gerryisrad/PocketReference/Docs/Documents & Advanced/PCB/SCRAPPED V3/EXPORTED SVG/3D_BACK.png

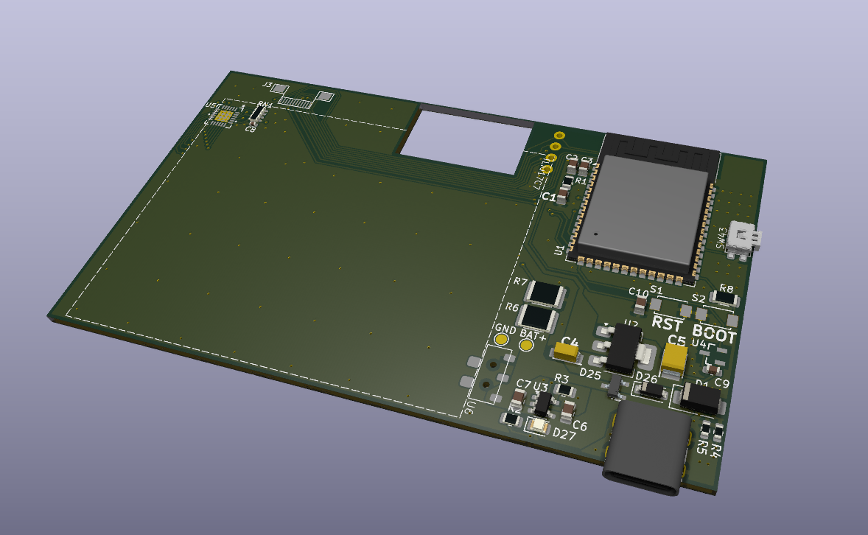
Docs/Documents & Advanced/PCB/SCRAPPED V3/EXPORTED SVG/3D_BACK.png
