gerryisrad/PocketReference/Docs/Documents & Advanced/PCB/V3.3/einkPDA_keyboard/EXPORTED SVG/3D_FRONT.png

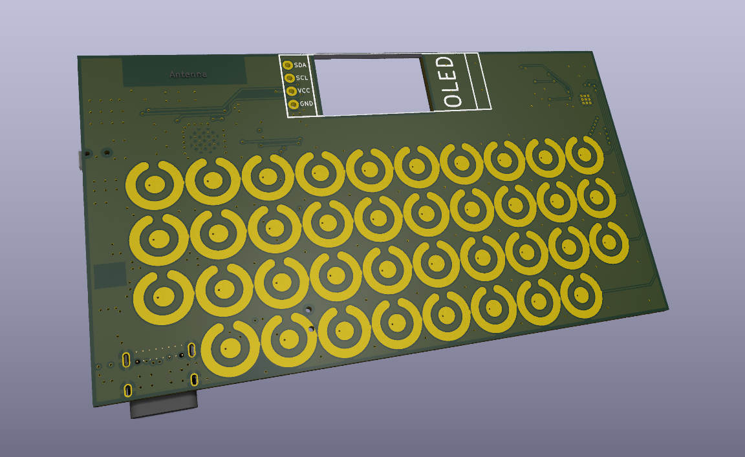
Docs/Documents & Advanced/PCB/V3.3/einkPDA_keyboard/EXPORTED SVG/3D_FRONT.png
