gerryisrad/PocketReference/Docs/Documents & Advanced/PCB/SCRAPPED V3/EXPORTED SVG/B_Cu.png

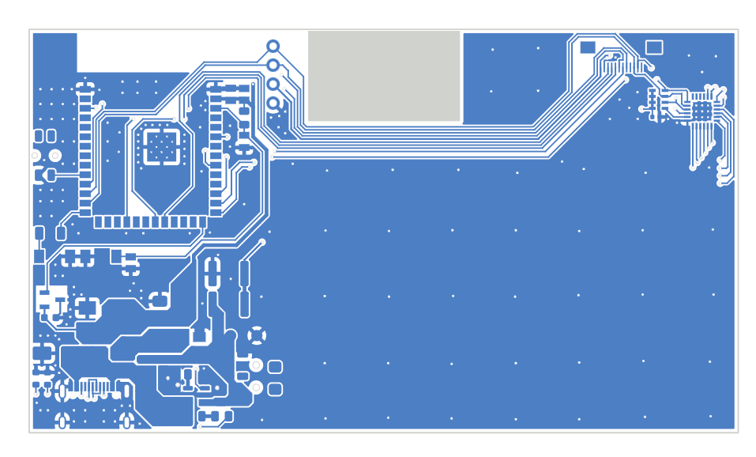
Docs/Documents & Advanced/PCB/SCRAPPED V3/EXPORTED SVG/B_Cu.png
