gerryisrad/PocketReference/Docs/Documents & Advanced/PCB/SCRAPPED V3/EXPORTED SVG/In1.png

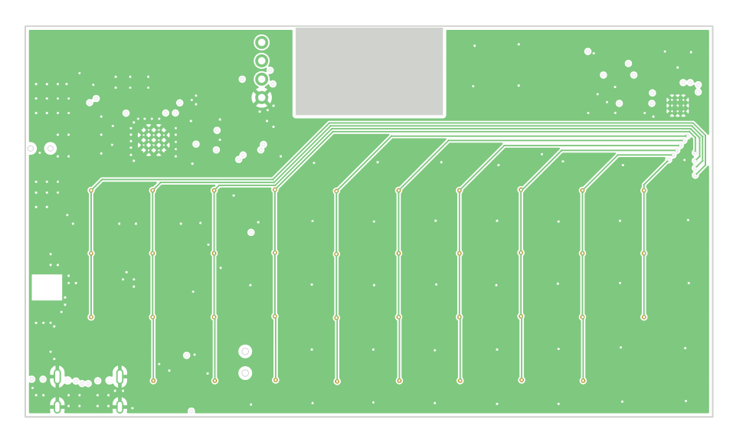
Docs/Documents & Advanced/PCB/SCRAPPED V3/EXPORTED SVG/In1.png
