gerryisrad/PocketReference/Docs/Documents & Advanced/PCB/SCRAPPED V3/EXPORTED SVG/Layout.png

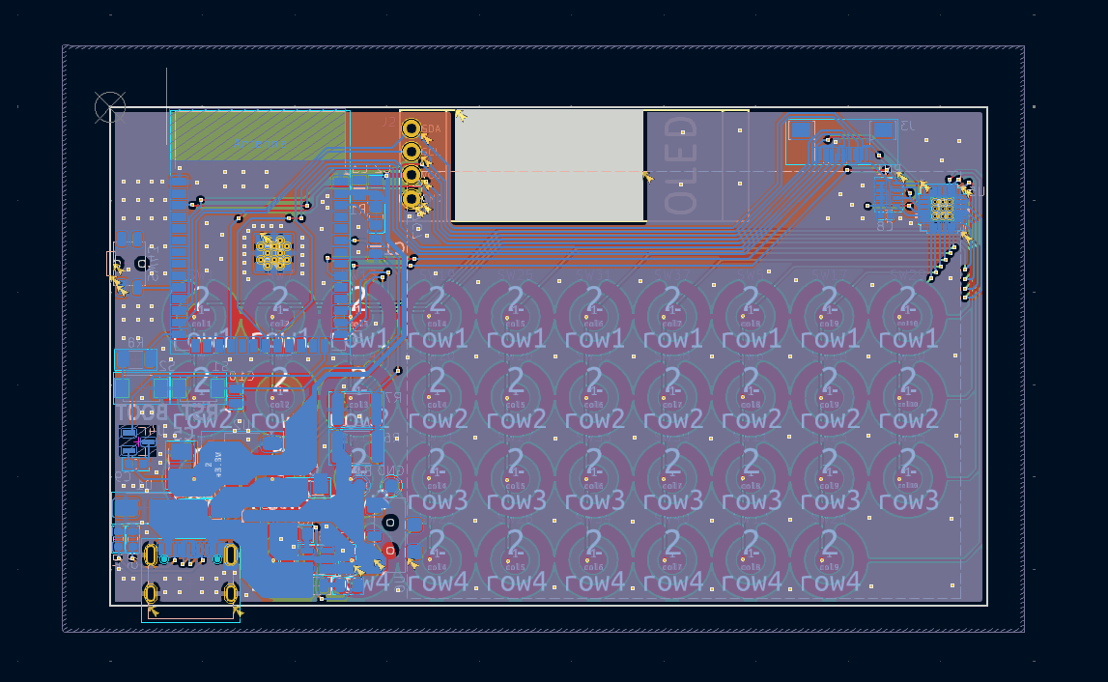
Docs/Documents & Advanced/PCB/SCRAPPED V3/EXPORTED SVG/Layout.png
