gerryisrad/PocketReference/Docs/Documents & Advanced/PCB/V3.2 - Copy/PCB_V3.2.pdf

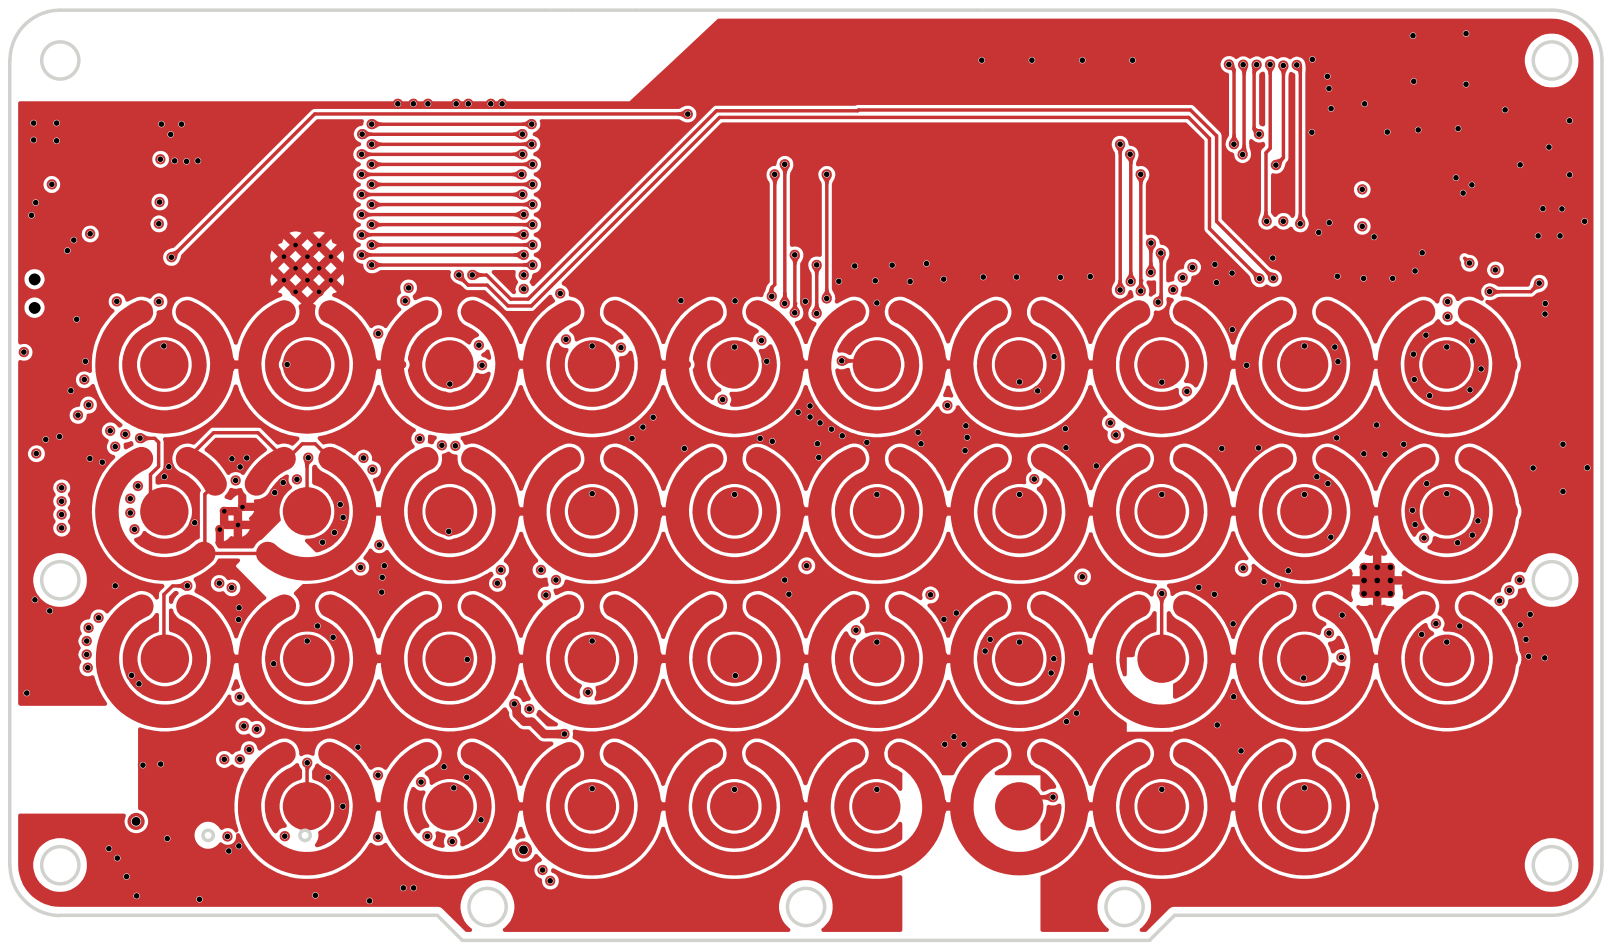
[picture p16: page 1]

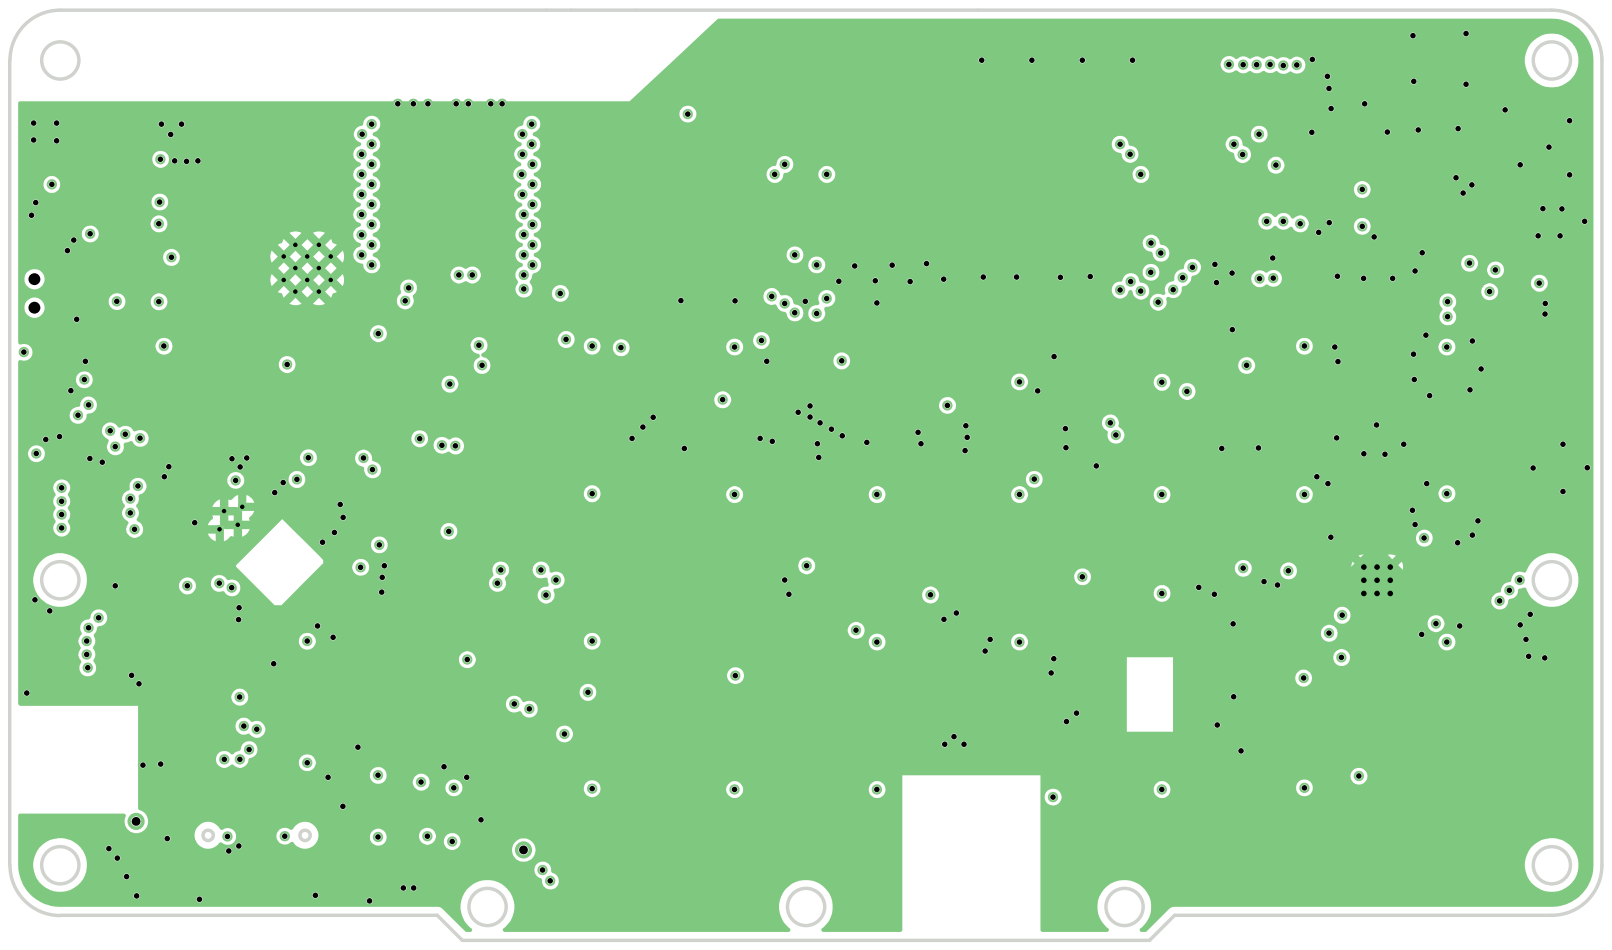
[picture p17: page 2]

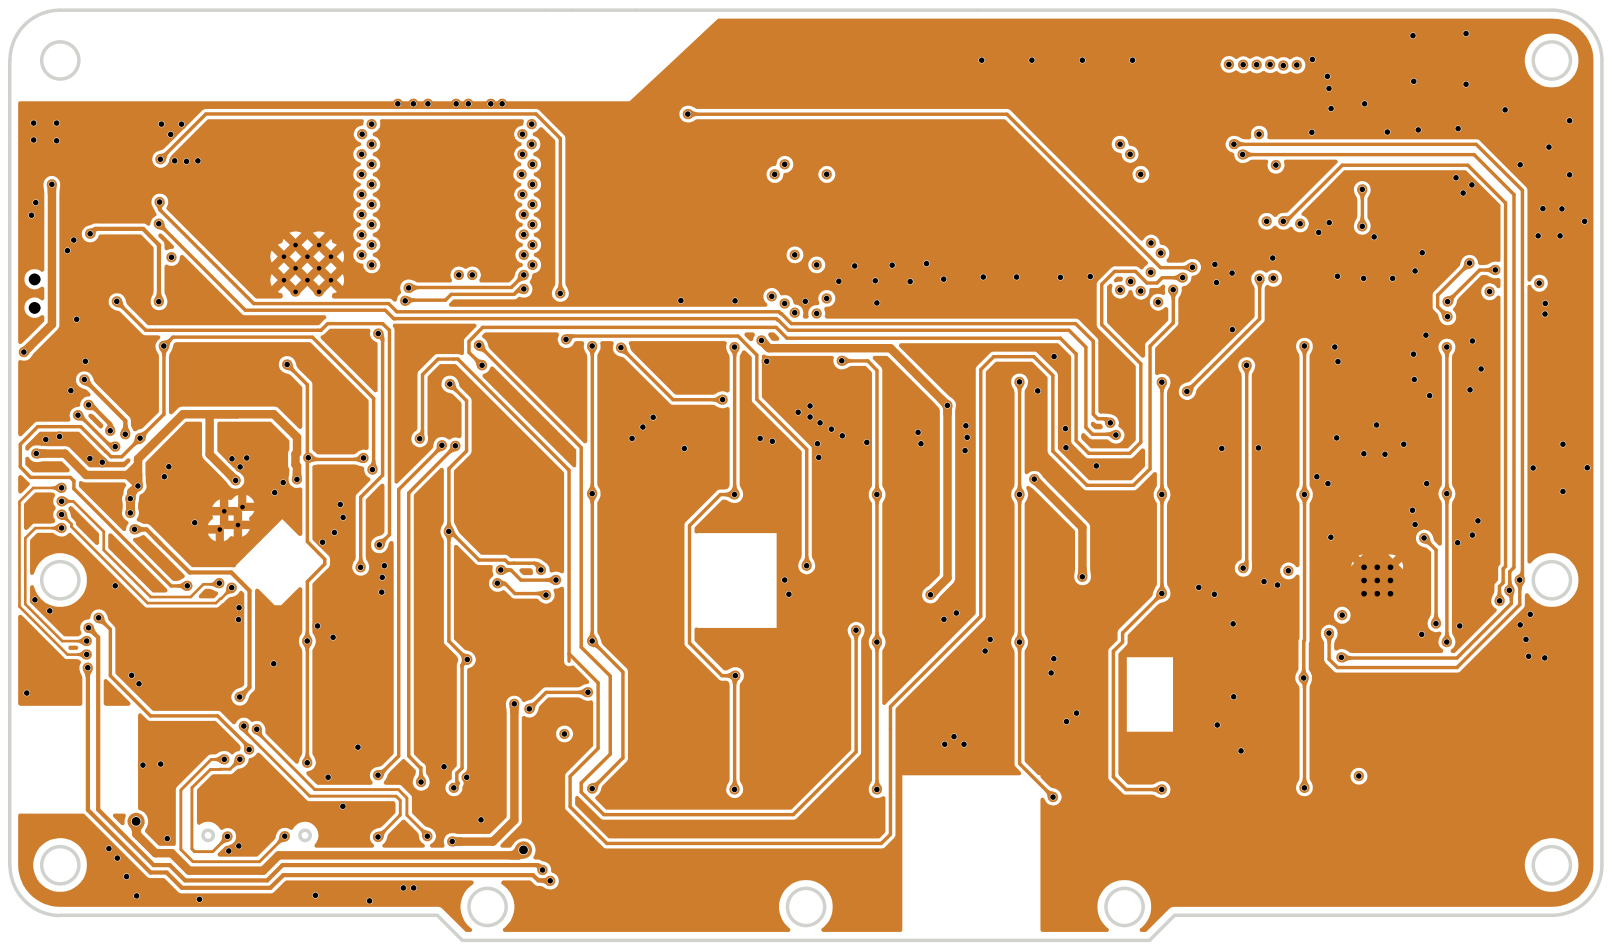
[picture p18: page 3]

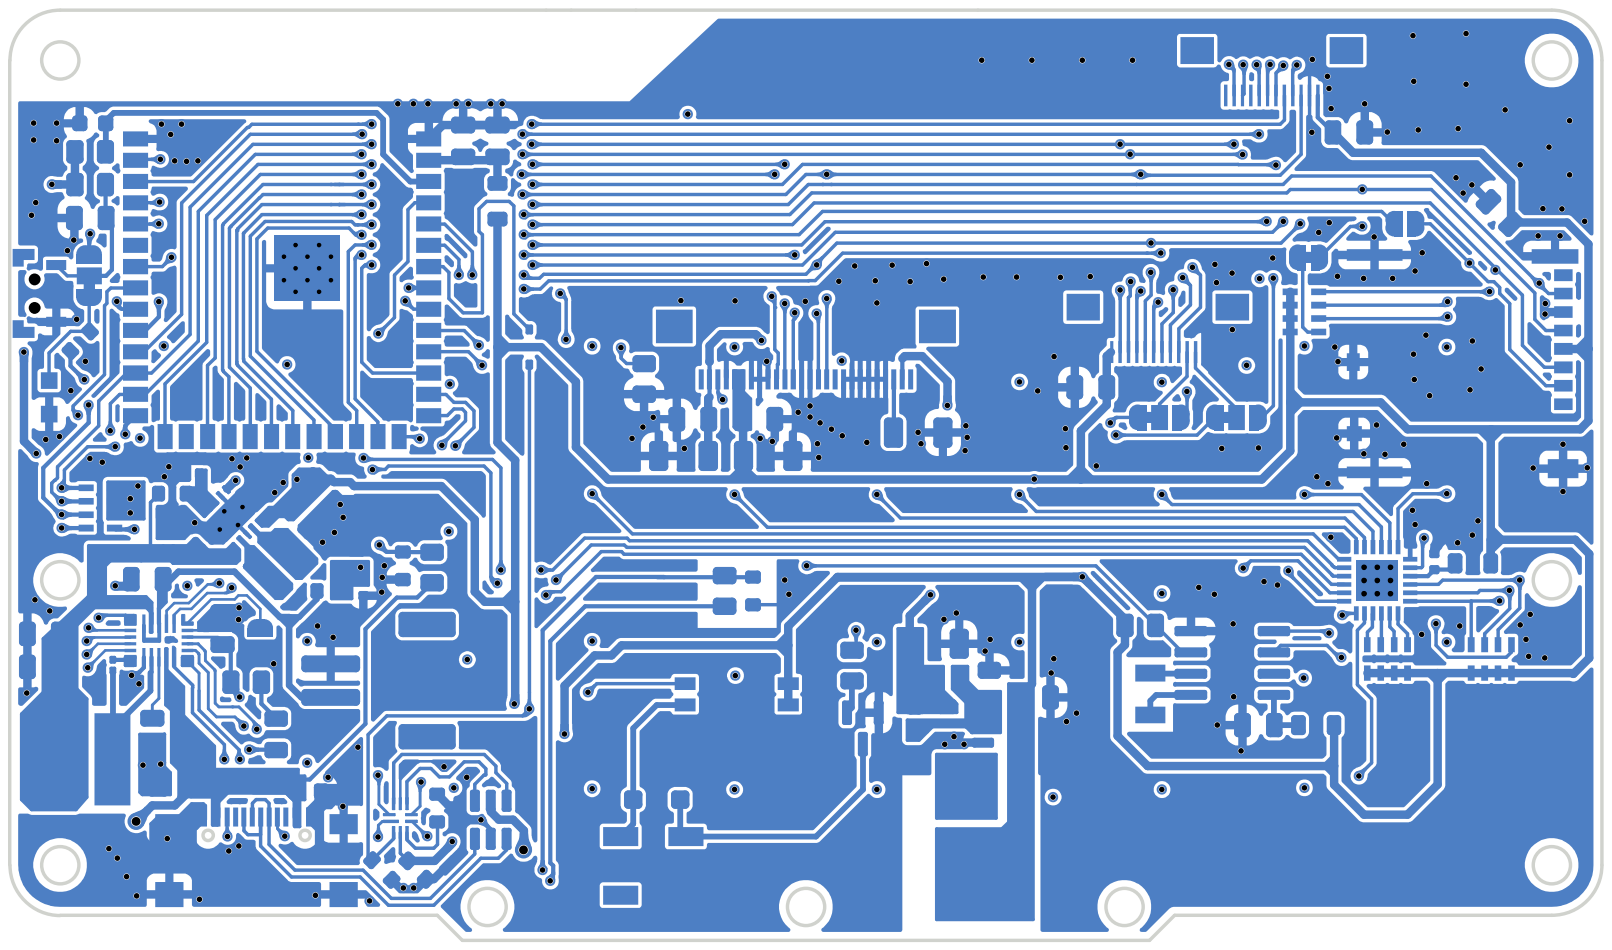
[picture p19: page 4]

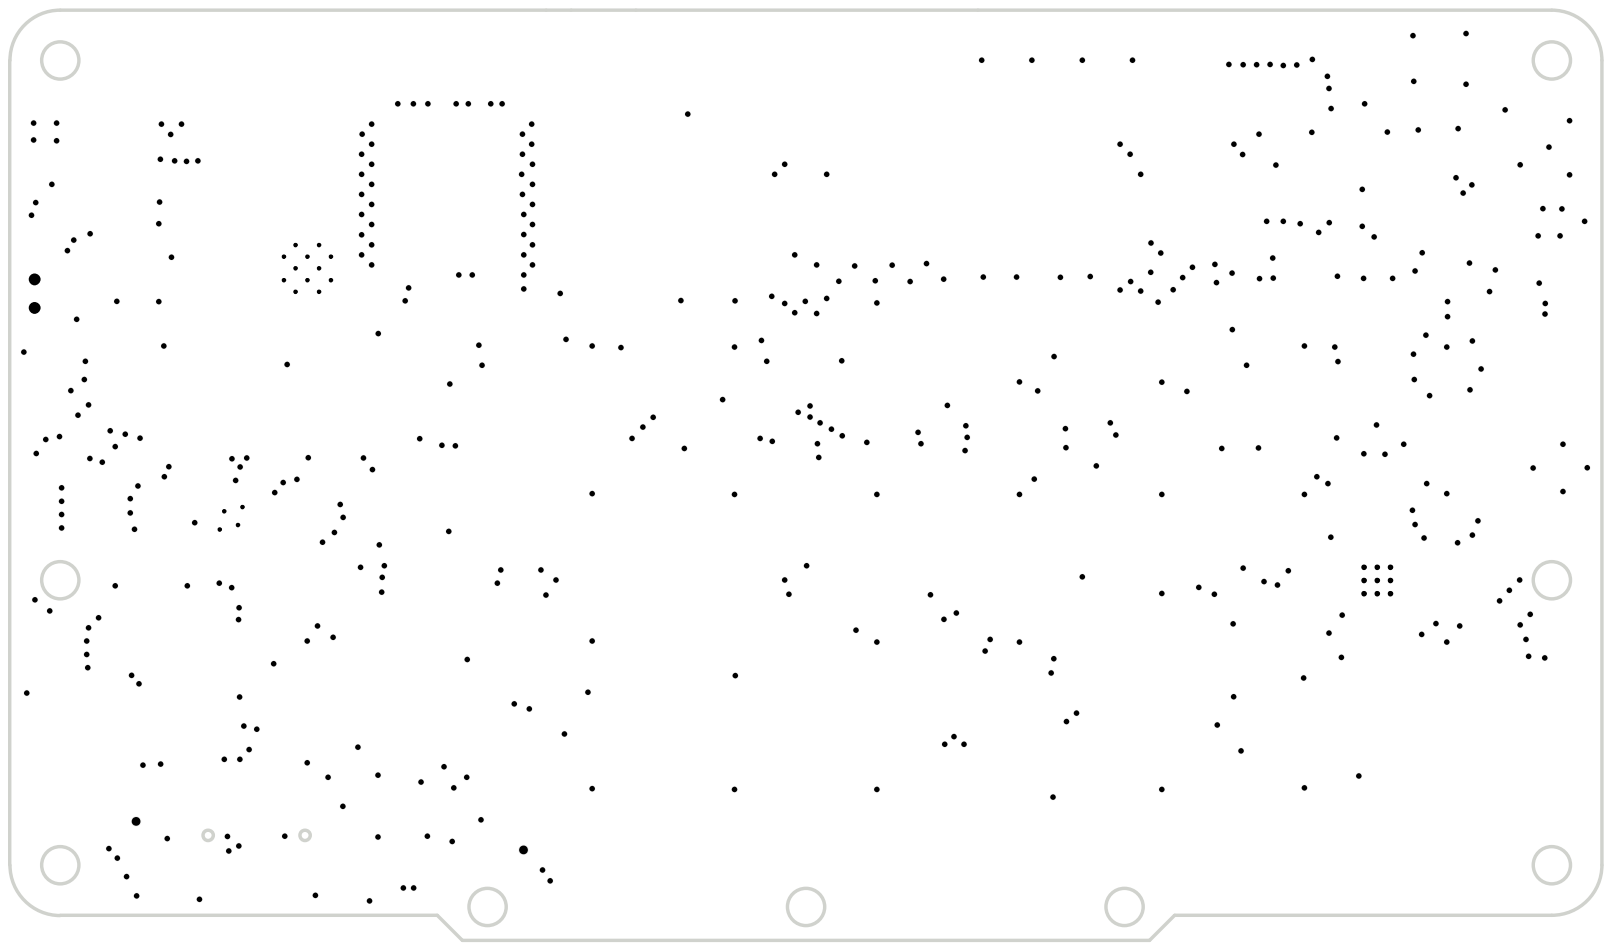
[picture p20: page 5]

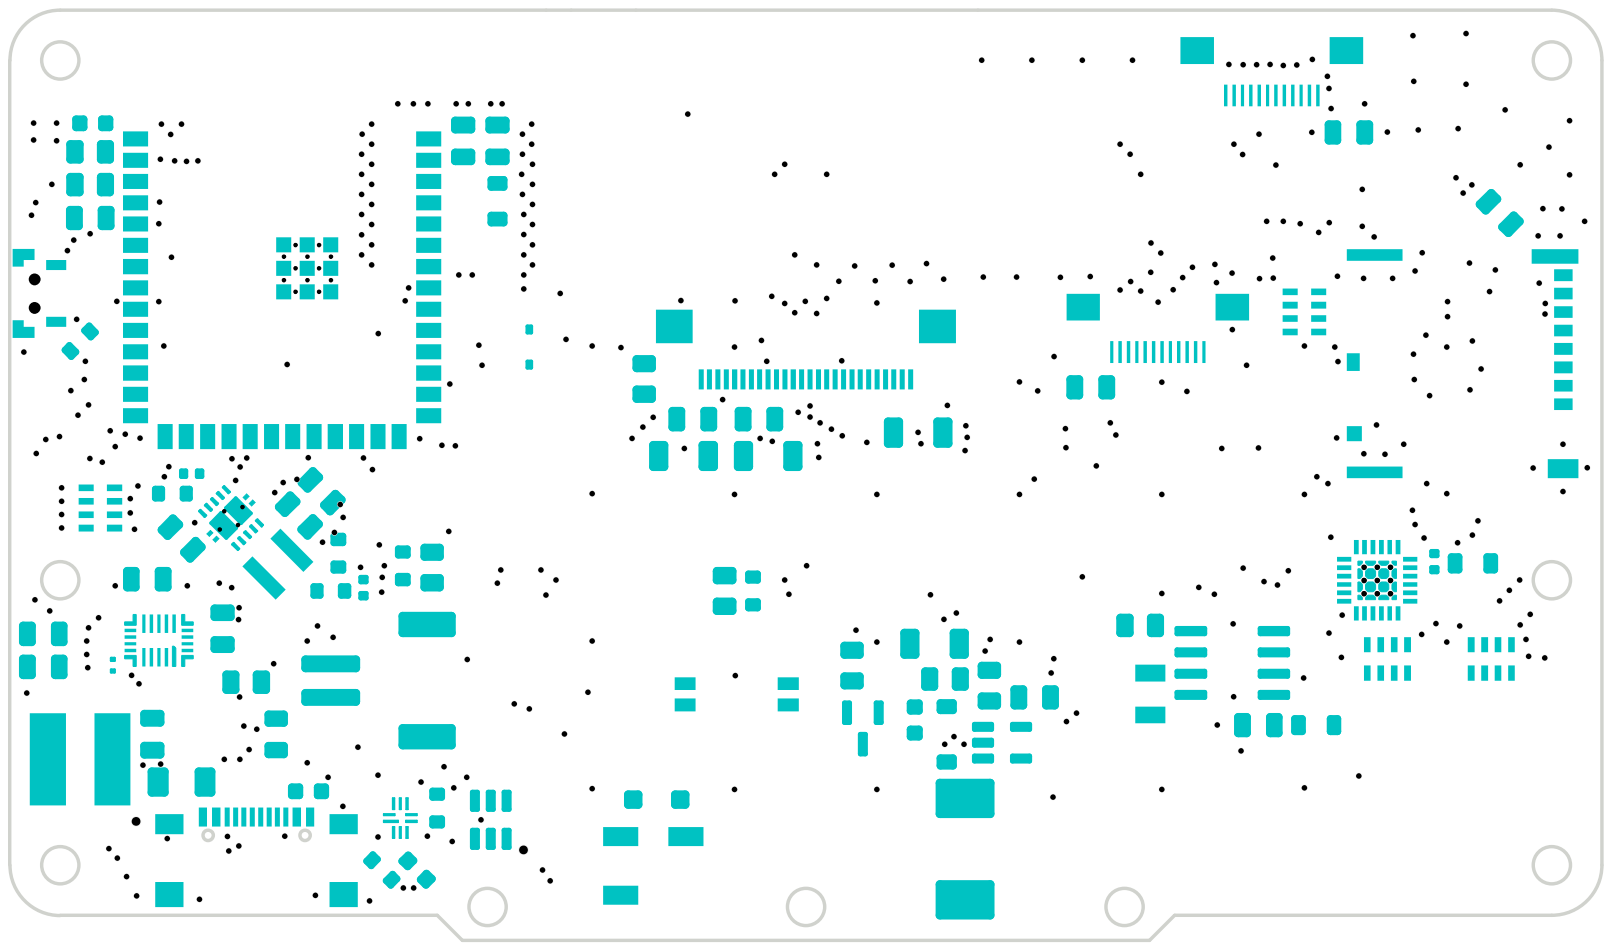
[picture p21: page 6]

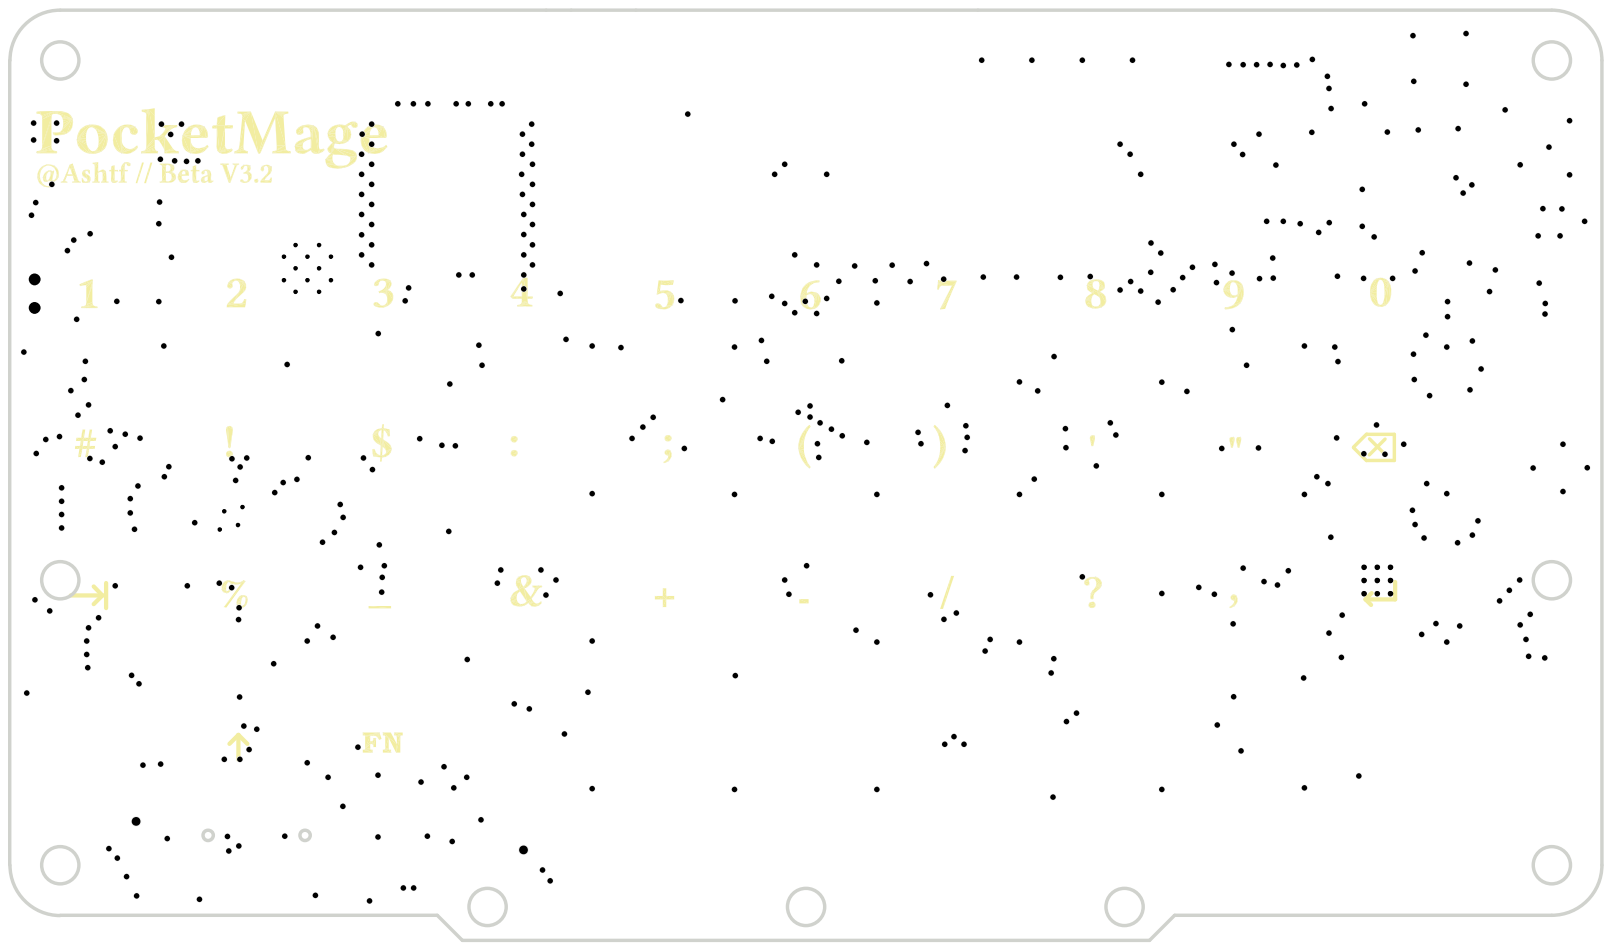
[picture p22: page 7]

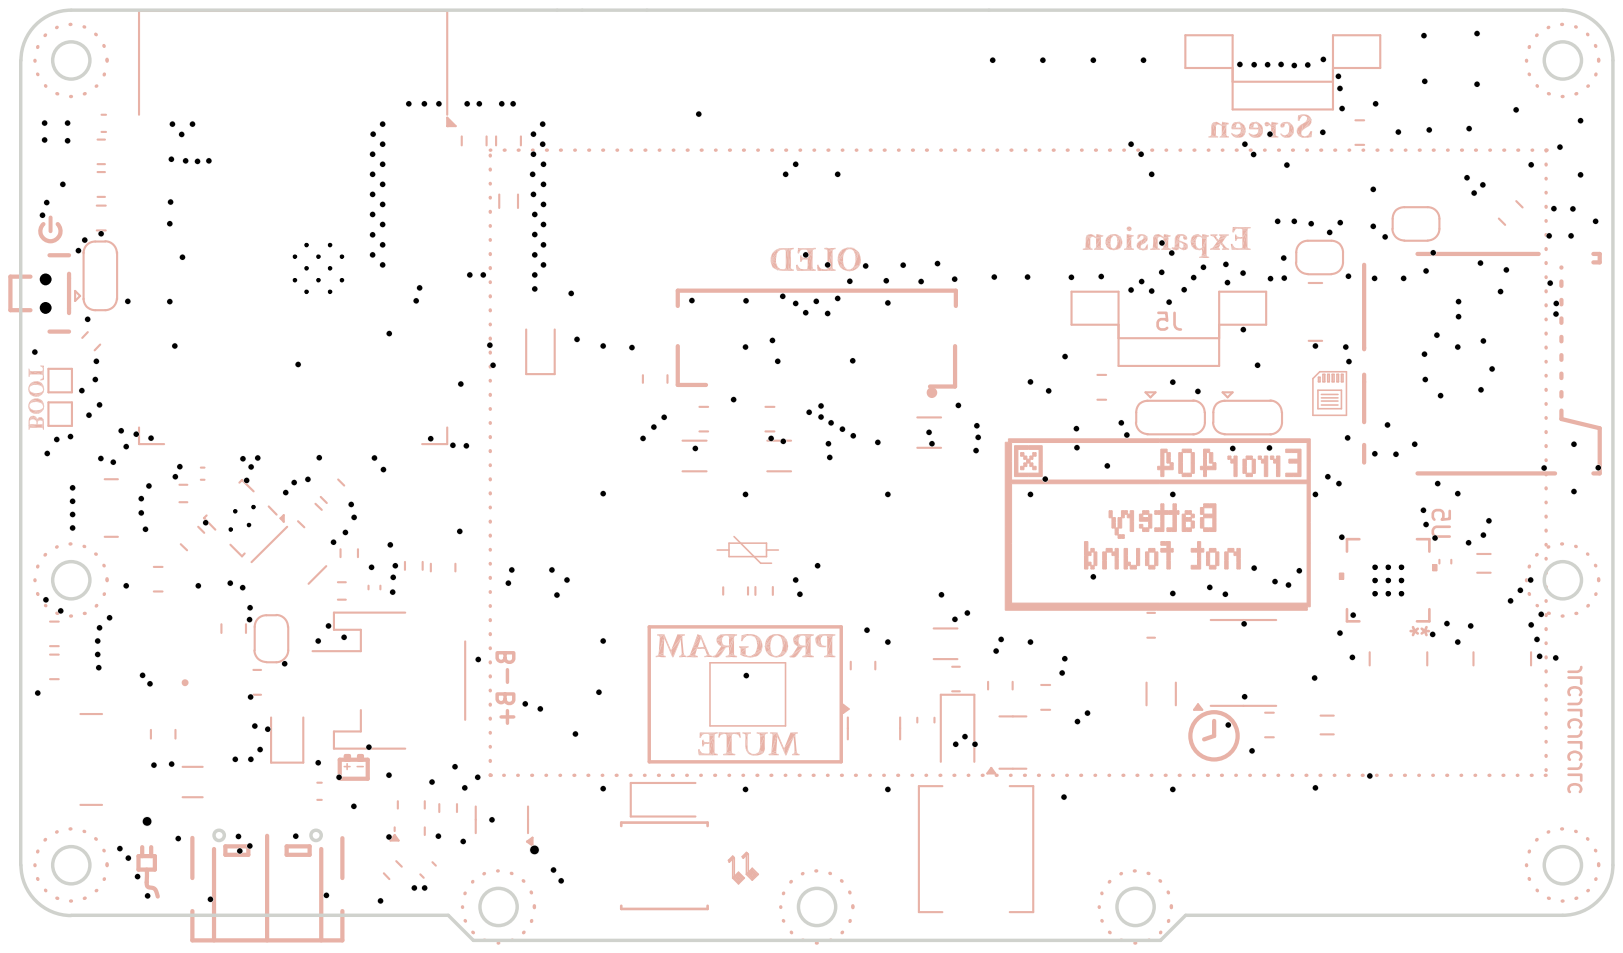
[picture p23: page 8]

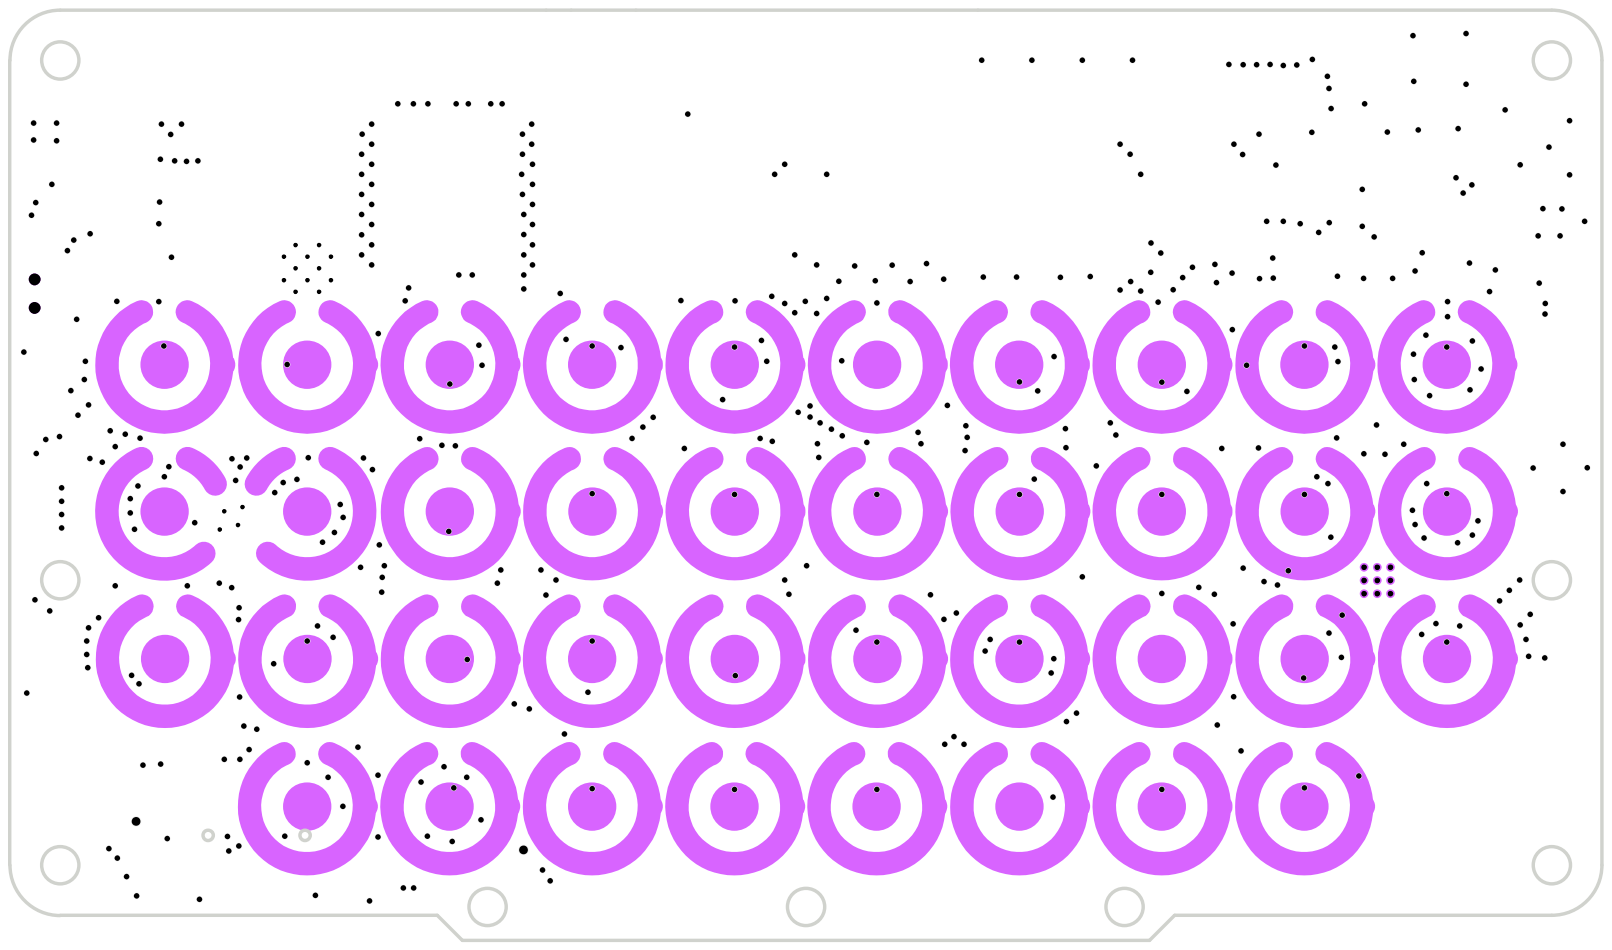
[picture p24: page 9]

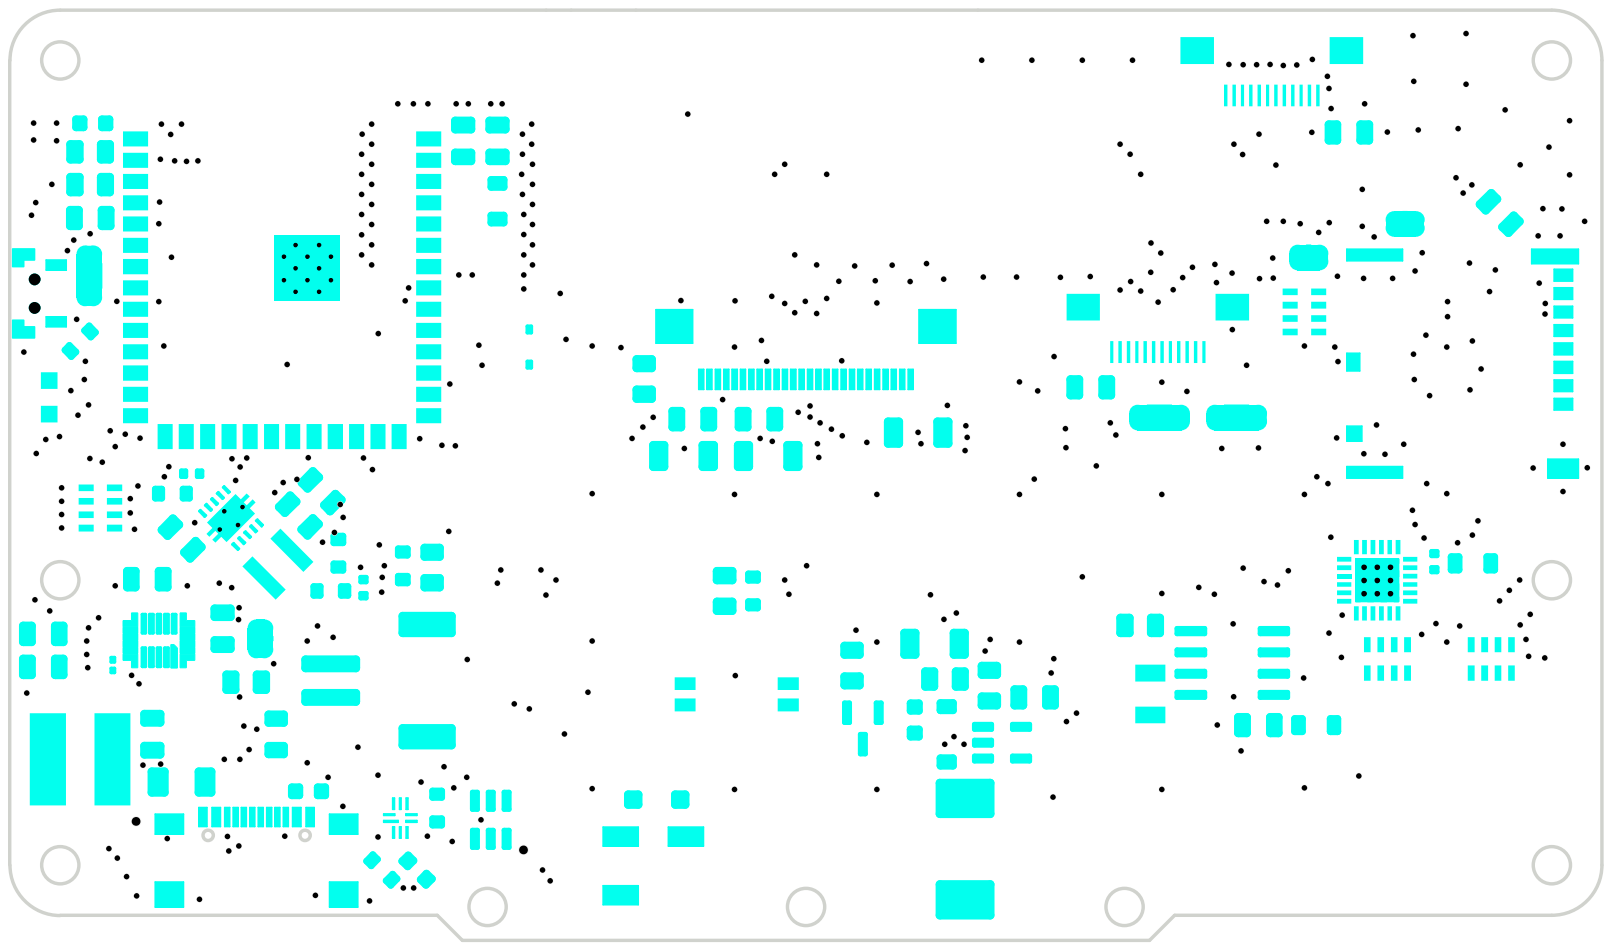
[picture p25: page 10]
