gerryisrad/PocketReference/Code/PocketMage_V3/src/OS_APPS/TXT.cpp

//  ooooooooooooo ooooooo  ooooo ooooooooooooo  //
//  8'   888   `8  `8888    d8'  8'   888   `8  //
//       888         Y888..8P         888       //
//       888          `8888'          888       //
//       888         .8PY888.         888       //
//       888        d8'  `888b        888       //
//      o888o     o888o  o88888o     o888o      //

#include <globals.h>
#if !OTA_APP // POCKETMAGE_OS
enum TXTState { TXT_, WIZ0, WIZ1, WIZ2, WIZ3, FONT };
TXTState CurrentTXTState = TXT_;

static String currentWord = "";
String outLines[13];
String prevEditingFile = "";
static String currentLine = "";
static volatile bool doFull = false;


void TXT_INIT_OLD() {
  if (PM_SDAUTO().getEditingFile() != "") PM_SDAUTO().loadFile();
  CurrentAppState = TXT;
  CurrentTXTState = TXT_;
  KB().setKeyboardState(NORMAL);
  TOUCH().setDynamicScroll(0);
  newLineAdded = true;
}

void processKB_TXT_OLD() {
  OLED().setPowerSave(false);
  
  disableTimeout = false;

  unsigned long currentMillis = millis();
  if (currentMillis - KBBounceMillis >= KB_COOLDOWN) {  
    char inchar = KB().updateKeypress();
    switch (CurrentTXTState) {
      case TXT_:
        // SET MAXIMUMS AND FONT
        EINK().setTXTFont(EINK().getCurrentFont());

        // UPDATE SCROLLBAR
        TOUCH().updateScrollFromTouch();

        // HANDLE INPUTS
        //No char recieved
        if (inchar == 0);  
        else if (inchar == 12) {
          CurrentAppState = HOME;
          currentLine     = "";
          newState        = true;
          KB().setKeyboardState(NORMAL);
        }
        //TAB Recieved
        else if (inchar == 9) {                                  
          currentLine += "    ";
        }                                      
        //SHIFT Recieved
        else if (inchar == 17) {                                  
          if (KB().getKeyboardState() == SHIFT || KB().getKeyboardState() == FN_SHIFT) {
            KB().setKeyboardState(NORMAL);
          } else if (KB().getKeyboardState() == FUNC) {
            KB().setKeyboardState(FN_SHIFT);
          } else {
            KB().setKeyboardState(SHIFT);
          }
        }
        //FN Recieved
        else if (inchar == 18) {                                  
          if (KB().getKeyboardState() == FUNC || KB().getKeyboardState() == FN_SHIFT) {
            KB().setKeyboardState(NORMAL);
          } else if (KB().getKeyboardState() == SHIFT) {
            KB().setKeyboardState(FN_SHIFT);
          } else {
            KB().setKeyboardState(FUNC);
          }
        }
        //Space Recieved
        else if (inchar == 32) {                                  
          currentLine += " ";
        }
        //CR Recieved
        else if (inchar == 13) {                          
          allLines.push_back(currentLine);
          currentLine = "";
          newLineAdded = true;
        }
        //ESC / CLEAR Recieved
        else if (inchar == 20) {                                  
          allLines.clear();
          currentLine = "";
          OLED().oledWord("Clearing...");
          doFull = true;
          newLineAdded = true;
          delay(300);
        }
        // LEFT
        else if (inchar == 19) {                                  
          
        }
        // RIGHT
        else if (inchar == 21) {                                  
          
        }
        //BKSP Recieved
        else if (inchar == 8) {                  
          if (currentLine.length() > 0) {
            currentLine.remove(currentLine.length() - 1);
          }
        }
        //SAVE Recieved
        else if (inchar == 6) {
          //File exists, save normally
          if (PM_SDAUTO().getEditingFile() != "" && PM_SDAUTO().getEditingFile() != "-") {
            PM_SDAUTO().saveFile();
            KB().setKeyboardState(NORMAL);
            newLineAdded = true;
          }
          //File does not exist, make a new one
          else {
            CurrentTXTState = WIZ3;
            currentLine = "";
            KB().setKeyboardState(NORMAL);
            doFull = true;
            newState = true;
          }
        }
        //LOAD Recieved
        else if (inchar == 5) {
          PM_SDAUTO().loadFile();
          KB().setKeyboardState(NORMAL);
          newLineAdded = true;
        }
        //FILE Recieved
        else if (inchar == 7) {
          CurrentTXTState = WIZ0;
          KB().setKeyboardState(NORMAL);
          newState = true;
        }
        // Font Switcher 
        else if (inchar == 14) {                                  
          CurrentTXTState = FONT;
          KB().setKeyboardState(FUNC);
          newState = true;
        }
        else {
          currentLine += inchar;
          if (inchar >= 48 && inchar <= 57) {}  //Only leave FN on if typing numbers
          else if (KB().getKeyboardState() != NORMAL) {
            KB().setKeyboardState(NORMAL);
          }
        }

        currentMillis = millis();
        //Make sure oled only updates at 60fps
        if (currentMillis - OLEDFPSMillis >= (1000/60)) {
          OLEDFPSMillis = currentMillis;
          // ONLY SHOW OLEDLINE WHEN NOT IN SCROLL MODE
          if (TOUCH().getLastTouch() == -1) {
            OLED().oledLine(currentLine, currentLine.length());
            if (TOUCH().getPrevDynamicScroll() != TOUCH().getDynamicScroll()) TOUCH().setPrevDynamicScroll(TOUCH().getDynamicScroll());
          }
          else OLED().oledScroll();
        }

        if (currentLine.length() > 0) {
          int16_t x1, y1;
          uint16_t charWidth, charHeight;
          display.getTextBounds(currentLine, 0, 0, &x1, &y1, &charWidth, &charHeight);

          if (charWidth >= display.width()-5) {
            // If currentLine ends with a space, just start a new line
            if (currentLine.endsWith(" ")) {
              allLines.push_back(currentLine);
              currentLine = "";
            }
            // If currentLine ends with a letter, we are in the middle of a word
            else {
              int lastSpace = currentLine.lastIndexOf(' ');
              String partialWord;

              if (lastSpace != -1) {
                partialWord = currentLine.substring(lastSpace + 1);
                currentLine = currentLine.substring(0, lastSpace);  // Strip partial word
                allLines.push_back(currentLine);
                currentLine = partialWord;  // Start new line with the partial word
              } 
              // No spaces found, whole line is a single word
              else {
                allLines.push_back(currentLine);
                currentLine = "";
              }
            }
            newLineAdded = true;
          }
        }

        break;
      case WIZ0:
        //No char recieved
        if (inchar == 0);
        //BKSP Recieved
        else if (inchar == 127 || inchar == 8) {                  
          CurrentTXTState = TXT_;
          KB().setKeyboardState(NORMAL);
          newLineAdded = true;
          currentWord = "";
          currentLine = "";
          display.fillScreen(GxEPD_WHITE);
        }
        else if (inchar >= '0' && inchar <= '9'){
          int fileIndex = (inchar == '0') ? 10 : (inchar - '0');
          //Edit a new file
          if (PM_SDAUTO().getFilesListIndex(fileIndex - 1) != PM_SDAUTO().getEditingFile()) { 
            //Selected file does not exist, create a new one
            if (PM_SDAUTO().getFilesListIndex(fileIndex - 1) == "-") {
              CurrentTXTState = WIZ3;
              EINK().setFullRefreshAfter(FULL_REFRESH_AFTER + 1);
              newState = true;
              display.fillScreen(GxEPD_WHITE);
            }
            //Selected file exists, prompt to save current file
            else {      
              prevEditingFile = PM_SDAUTO().getEditingFile();
              PM_SDAUTO().setEditingFile(PM_SDAUTO().getFilesListIndex(fileIndex - 1));      
              CurrentTXTState = WIZ1;
              EINK().setFullRefreshAfter(FULL_REFRESH_AFTER + 1);
              newState = true;
              display.fillScreen(GxEPD_WHITE);
            }
          }
          //Selected file is current file, return to editor
          else {
            KB().setKeyboardState(NORMAL);
            CurrentTXTState = TXT_;
            newLineAdded = true;
            currentWord = "";
            currentLine = "";
            display.fillScreen(GxEPD_WHITE);
          }

        }

        currentMillis = millis();
        //Make sure oled only updates at 60fps
        if (currentMillis - OLEDFPSMillis >= (1000/OLED_MAX_FPS)) {
          OLEDFPSMillis = currentMillis;
          OLED().oledLine(currentWord, currentWord.length(),false);
        }
        break;
      case WIZ1:
        //No char recieved
        if (inchar == 0);
        //BKSP Recieved
        else if (inchar == 127 || inchar == 8) {                  
          CurrentTXTState = WIZ0;
          KB().setKeyboardState(FUNC);
          EINK().setFullRefreshAfter(FULL_REFRESH_AFTER + 1);
          newState = true;
          display.fillScreen(GxEPD_WHITE);
        }
        else if (inchar >= '0' && inchar <= '9'){
          int numSelect = (inchar == '0') ? 10 : (inchar - '0');
          //YES (save current file)
          if (numSelect == 1) {
            //File to be saved does not exist
            if (prevEditingFile == "" || prevEditingFile == "-") {
              CurrentTXTState = WIZ2;
              currentWord = "";
              KB().setKeyboardState(NORMAL);
              EINK().setFullRefreshAfter(FULL_REFRESH_AFTER + 1);
              newState = true;
              display.fillScreen(GxEPD_WHITE);
            }
            //File to be saved exists
            else {
              //Save current file
              PM_SDAUTO().saveFile();

              delay(200);
              //Load new file
              PM_SDAUTO().loadFile();
              //Return to TXT
              CurrentTXTState = TXT_;
              KB().setKeyboardState(NORMAL);
              newLineAdded = true;
              currentWord = "";
              currentLine = "";
              display.fillScreen(GxEPD_WHITE);
            }
          }
          //NO  (don't save current file)
          else if (numSelect == 2) {
            //Just load new file
            PM_SDAUTO().loadFile();
            //Return to TXT
            CurrentTXTState = TXT_;
            KB().setKeyboardState(NORMAL);
            newLineAdded = true;
            currentWord = "";
            currentLine = "";
            display.fillScreen(GxEPD_WHITE);
          }
        }

        currentMillis = millis();
        //Make sure oled only updates at 60fps
        if (currentMillis - OLEDFPSMillis >= (1000/OLED_MAX_FPS)) {
          OLEDFPSMillis = currentMillis;
          OLED().oledLine(currentWord, currentWord.length(), false);
        }
        break;

      case WIZ2:
        //No char recieved
        if (inchar == 0);                                         
        //SHIFT Recieved
        else if (inchar == 17) {                                  
          if (KB().getKeyboardState() == SHIFT || KB().getKeyboardState() == FN_SHIFT) {
            KB().setKeyboardState(NORMAL);
          } else if (KB().getKeyboardState() == FUNC) {
            KB().setKeyboardState(FN_SHIFT);
          } else {
            KB().setKeyboardState(SHIFT);
          }
          newState = true;
        }
        //FN Recieved
        else if (inchar == 18) {                                  
          if (KB().getKeyboardState() == FUNC || KB().getKeyboardState() == FN_SHIFT) {
            KB().setKeyboardState(NORMAL);
          } else if (KB().getKeyboardState() == SHIFT) {
            KB().setKeyboardState(FN_SHIFT);
          } else {
            KB().setKeyboardState(FUNC);
          }
          newState = true;
        }
        //Space Recieved
        else if (inchar == 32) {}
        //ESC / CLEAR Recieved
        else if (inchar == 20) {                                  
          currentWord = "";
        }
        //BKSP Recieved
        else if (inchar == 8) {                  
          if (currentWord.length() > 0) {
            currentWord.remove(currentWord.length() - 1);
          }
        }
        //ENTER Recieved
        else if (inchar == 13) {                          
          prevEditingFile = "/" + currentWord + ".txt";

          //Save the file
          PM_SDAUTO().saveFile();

          delay(200);
          //Load new file
          PM_SDAUTO().loadFile();

          keypad.enableInterrupts();

          //Return to TXT_
          CurrentTXTState = TXT_;
          KB().setKeyboardState(NORMAL);
          newLineAdded = true;
          currentWord = "";
          currentLine = "";
        }
        //All other chars
        else {
          //Only allow char to be added if it's an allowed char
          if (isalnum(inchar) || inchar == '_' || inchar == '-' || inchar == '.') currentWord += inchar;
          if (inchar >= 48 && inchar <= 57) {}  //Only leave FN on if typing numbers
          else if (KB().getKeyboardState() != NORMAL){
            KB().setKeyboardState(NORMAL);
          }
        }

        currentMillis = millis();
        //Make sure oled only updates at 60fps
        if (currentMillis - OLEDFPSMillis >= (1000/OLED_MAX_FPS)) {
          OLEDFPSMillis = currentMillis;
          OLED().oledLine(currentWord, currentWord.length(), false);
        }
        break;
      case WIZ3:
        //No char recieved
        if (inchar == 0);                                         
        //SHIFT Recieved
        else if (inchar == 17) {                                  
          if (KB().getKeyboardState() == SHIFT || KB().getKeyboardState() == FN_SHIFT) {
            KB().setKeyboardState(NORMAL);
          } else if (KB().getKeyboardState() == FUNC) {
            KB().setKeyboardState(FN_SHIFT);
          } else {
            KB().setKeyboardState(SHIFT);
          }
        }
        //FN Recieved
        else if (inchar == 18) {                                  
          if (KB().getKeyboardState() == FUNC || KB().getKeyboardState() == FN_SHIFT) {
            KB().setKeyboardState(NORMAL);
          } else if (KB().getKeyboardState() == SHIFT) {
            KB().setKeyboardState(FN_SHIFT);
          } else {
            KB().setKeyboardState(FUNC);
          }
        }
        //Space Recieved
        else if (inchar == 32) {}
        //ESC / CLEAR Recieved
        else if (inchar == 20) {                                  
          currentWord = "";
        }
        //BKSP Recieved
        else if (inchar == 8) {                  
          if (currentWord.length() > 0) {
            currentWord.remove(currentWord.length() - 1);
          }
        }
        //ENTER Recieved
        else if (inchar == 13) {                          
          prevEditingFile = "/" + currentWord + ".txt";

          //Save the file
          PM_SDAUTO().saveFile();
          //Ask to save prev file
          
          //Return to TXT_
          CurrentTXTState = TXT_;
          KB().setKeyboardState(NORMAL);
          newLineAdded = true;
          currentWord = "";
          currentLine = "";
        }
        //All other chars
        else {
          //Only allow char to be added if it's an allowed char
          if (isalnum(inchar) || inchar == '_' || inchar == '-' || inchar == '.') currentWord += inchar;
          if (inchar >= 48 && inchar <= 57) {}  //Only leave FN on if typing numbers
          else if (KB().getKeyboardState() != NORMAL){
            KB().setKeyboardState(NORMAL);
          }
        }

        currentMillis = millis();
        //Make sure oled only updates at 60fps
        if (currentMillis - OLEDFPSMillis >= (1000/OLED_MAX_FPS)) {
          OLEDFPSMillis = currentMillis;
          OLED().oledLine(currentWord, currentWord.length(), false);
        }
        break;
      case FONT:
        //No char recieved
        if (inchar == 0);
        //BKSP Recieved
        else if (inchar == 127 || inchar == 8) {                  
          CurrentTXTState = TXT_;
          KB().setKeyboardState(NORMAL);
          newLineAdded = true;
          currentWord = "";
          currentLine = "";
          display.fillScreen(GxEPD_WHITE);
        }
        else if (inchar >= '0' && inchar <= '9') {
          int fontIndex = (inchar == '0') ? 10 : (inchar - '0');
          switch (fontIndex) {
            case 1:
              EINK().setCurrentFont(&FreeMonoBold9pt7b);
              break;
            case 2:
              EINK().setCurrentFont(&FreeSans9pt7b);
              break;
            case 3:
              EINK().setCurrentFont(&FreeSerif9pt7b);
              break;
            case 4:
              EINK().setCurrentFont(&FreeSerifBold9pt7b);
              break;
            case 5:
              EINK().setCurrentFont(&FreeMono12pt7b);
              break;
            case 6:
              EINK().setCurrentFont(&FreeSans12pt7b);
              break;
            case 7:
              EINK().setCurrentFont(&FreeSerif12pt7b);
              break;
            default:
              EINK().setCurrentFont(&FreeMonoBold9pt7b);
              break;
          }
          // SET THE FONT
          EINK().setTXTFont(EINK().getCurrentFont());

          // UPDATE THE ARRAY TO MATCH NEW FONT SIZE
          String fullTextStr = vectorToString();
          stringToVector(fullTextStr);

          CurrentTXTState = TXT_;
          KB().setKeyboardState(NORMAL);
          newLineAdded = true;
          currentWord = "";
          currentLine = "";
          display.fillScreen(GxEPD_WHITE);
        }

        currentMillis = millis();
        //Make sure oled only updates at 60fps
        if (currentMillis - OLEDFPSMillis >= (1000/OLED_MAX_FPS)) {
          OLEDFPSMillis = currentMillis;
          OLED().oledLine(currentWord, currentWord.length(), false);
        }
        break;

    }
    KBBounceMillis = currentMillis;
  }
}

void einkHandler_TXT_OLD() {
  if (newLineAdded || newState) {
    switch (CurrentTXTState) {
      case TXT_:
        if (newState && doFull) {
          EINK().resetDisplay();
          EINK().refresh();
        }
        if (newLineAdded && !newState) {
          EINK().einkTextDynamic(true);
          EINK().refresh();
        }
        break;
      case WIZ0:
        display.setFullWindow();
        EINK().einkTextDynamic(true, true);      
        display.setFont(&FreeMonoBold9pt7b);
        
        display.fillRect(0,display.height()-26,display.width(),26,GxEPD_WHITE);
        display.drawRect(0,display.height()-20,display.width(),20,GxEPD_BLACK);
        display.setCursor(4, display.height()-6);
        //display.print("W:" + String(countWords(allText)) + " C:" + String(countVisibleChars(allText)) + " L:" + String(EINK().countLines(allText)));
        display.drawBitmap(display.width()-30,display.height()-20, KBStatusallArray[6], 30, 20, GxEPD_BLACK);

        display.fillRect(60,0,200,218,GxEPD_WHITE);
        display.drawBitmap(60,0,fileWizLiteallArray[0],200,218, GxEPD_BLACK);

        keypad.disableInterrupts();
        PM_SDAUTO().listDir(*global_fs, "/");
        keypad.enableInterrupts();

        for (int i = 0; i < MAX_FILES; i++) {
          display.setCursor(88, 54+(17*i));
          display.print(PM_SDAUTO().getFilesListIndex(i));
        }

        EINK().refresh();
        KB().setKeyboardState(FUNC);
        break;
      case WIZ1:
        display.setFont(&FreeMonoBold9pt7b);
        
        display.fillRect(0,display.height()-26,display.width(),26,GxEPD_WHITE);
        display.drawRect(0,display.height()-20,display.width(),20,GxEPD_BLACK);
        display.setCursor(4, display.height()-6);
        //display.print("W:" + String(countWords(allText)) + " C:" + String(countVisibleChars(allText)) + " L:" + String(EINK().countLines(allText)));
        display.drawBitmap(display.width()-30,display.height()-20, KBStatusallArray[6], 30, 20, GxEPD_BLACK);

        display.fillRect(60,0,200,218,GxEPD_WHITE);
        display.drawBitmap(60,0,fileWizLiteallArray[1],200,218, GxEPD_BLACK);

        EINK().refresh();
        KB().setKeyboardState(FUNC);
        break;
      case WIZ2:
        display.setFont(&FreeMonoBold9pt7b);
        
        display.fillRect(0,display.height()-26,display.width(),26,GxEPD_WHITE);
        display.drawRect(0,display.height()-20,display.width(),20,GxEPD_BLACK);
        display.setCursor(4, display.height()-6);
        //display.print("W:" + String(countWords(allText)) + " C:" + String(countVisibleChars(allText)) + " L:" + String(EINK().countLines(allText)));
        display.drawBitmap(display.width()-30,display.height()-20, KBStatusallArray[6], 30, 20, GxEPD_BLACK);

        display.fillRect(60,0,200,218,GxEPD_WHITE);
        display.drawBitmap(60,0,fileWizLiteallArray[2],200,218, GxEPD_BLACK);

        EINK().refresh();
        KB().setKeyboardState(NORMAL);
        break;
      case WIZ3:
        display.setFullWindow();
        EINK().einkTextDynamic(true, true);      
        display.setFont(&FreeMonoBold9pt7b);
        
        display.fillRect(0,display.height()-26,display.width(),26,GxEPD_WHITE);
        display.drawRect(0,display.height()-20,display.width(),20,GxEPD_BLACK);
        display.setCursor(4, display.height()-6);
        //display.print("W:" + String(countWords(allText)) + " C:" + String(countVisibleChars(allText)) + " L:" + String(EINK().countLines(allText)));
        display.drawBitmap(display.width()-30,display.height()-20, KBStatusallArray[6], 30, 20, GxEPD_BLACK);

        display.fillRect(60,0,200,218,GxEPD_WHITE);
        display.drawBitmap(60,0,fileWizLiteallArray[3],200,218, GxEPD_BLACK);

        EINK().refresh();
        KB().setKeyboardState(NORMAL);
        break;
      case FONT:
        display.setFullWindow();
        EINK().einkTextDynamic(true, true);      
        
        EINK().drawStatusBar("Select a Font (0-9)");

        display.fillRect(60,0,200,218,GxEPD_WHITE);
        display.drawBitmap(60,0,fontfont0,200,218, GxEPD_BLACK);

        keypad.disableInterrupts();
        PM_SDAUTO().listDir(*global_fs, "/");
        keypad.enableInterrupts();

        for (int i = 0; i < 7; i++) {
          display.setCursor(88, 54+(17*i));
          switch (i) {
            case 0:
              display.setFont(&FreeMonoBold9pt7b);
              break;
            case 1:
              display.setFont(&FreeSans9pt7b);
              break;
            case 2:
              display.setFont(&FreeSerif9pt7b);
              break;
            case 3:
              display.setFont(&FreeSerifBold9pt7b);
              break;
            case 4:
              display.setFont(&FreeMono12pt7b);
              break;
            case 5:
              display.setFont(&FreeSans12pt7b);
              break;
            case 6:
              display.setFont(&FreeSerif12pt7b);
              break;
          }
          display.print("Font Number " + String(i+1));
        }

        EINK().refresh();
        KB().setKeyboardState(FUNC);
        break;
    
    }
    newState = false;
    newLineAdded = false;
  }
}
#endif
